lambdawolflabs/FWA-2022-Compass-ConBadge/hardware/design/sims/FWA_2020-2022_Compass_Charlieplex_LED_Currents.asc

19-337_BLU: LED; 19-337_BLU
19-337_GRN: LED; 19-337_GRN
19-337_RED: LED; 19-337_RED
IN-S63BT5UW: LED; IN-S63BT5UW
R1: res; {res}
R2: res; {res}
R3: res; {res}
R4: res; {res}
R5: res; {res}
R6: res; {res}
R7: res; {res}
R8: res; {res}
R9: res; {res}
R10: res; {res}
Resr1: res; {esr}
Resr2: res; {esr}
Resr3: res; {esr}
Resr4: res; {esr}
Resr5: res; {esr}
S1: sw; ATTINY_HS
S2: sw; ATTINY_LS
S3: sw; ATTINY_HS
S4: sw; ATTINY_LS
S5: sw; ATTINY_HS
S6: sw; ATTINY_LS
S7: sw; ATTINY_HS
S8: sw; ATTINY_LS
S9: sw; ATTINY_HS
S10: sw; ATTINY_LS
S11: sw; ATTINY_HS
S12: sw; ATTINY_LS
S13: sw; ATTINY_HS
S14: sw; ATTINY_LS
S15: sw; ATTINY_HS
S16: sw; ATTINY_LS
S17: sw; ATTINY_HS
S18: sw; ATTINY_LS
S19: sw; ATTINY_HS
S20: sw; ATTINY_LS
V1: voltage; 0
V2: voltage; 3
V3: voltage; 3
VLMTG1400: LED; VLMTG1400
Named nets: 0, VCC, L, R
.model ATTINY_HS SW(Ron=40 Roff=50Meg Vt=1.5)
.model ATTINY_LS SW(Roff=30 Ron=50Meg Vt=1.5)
.op
IN-S63BT5UW
VLMTG1400
19-337_RED
19-337_GRN
19-337_BLU
.model 19-337_RED D(Is=1.6137e-10 N=2.979)
.model 19-337_GRN D(Is=1.292e-6 N=7.532)
.model 19-337_BLU D(Is=2.7904E-5 N=9.056)
.MODEL IN-S63BT5UW D(Is=3.8462e-11 N=4.5828)
.MODEL VLMTG1400 D (Is=1.3882e-6 N=6.469)
.model ATTINY_HS_WC SW(Ron=80 Roff=50Meg Vt=1.5)
.model ATTINY_LS_WC SW(Roff=80 Ron=50Meg Vt=1.5)
.param res=82
.param esr=20
