lambdawolflabs/FWA-2022-Compass-ConBadge/hardware/design/sims/FWA_2020-2022_Compass_INT_MUX_Simulation.asc

B1: bv; V=V(VCC)*0.3
B2: bv; V=V(VCC)*0.7
R1: res; 20Meg
R1Leak: res; 20Meg
R2: res; 20Meg
R2Leak: res; 20Meg
R3: res; 1n
R3Leak: res; 20Meg
R4Leak: res; 20Meg
R5Leak: res; 20Meg
R6Leak: res; 20Meg
R13: res; {mc(27k,0.01)}
R14: res; {mc(4.7k,0.012)}
R15: res; {mc(7.5k,0.012)}
S1: sw; LS
S2: sw; LS
S4: sw; LS
V1: voltage; PULSE(3 0 0.5 1n 1n 1 2 2)
V2: voltage; PULSE(3 0 1 1n 1n 1 2 2)
V3: voltage; 3
V4: voltage; PULSE(3 0 0.25 1n 1n 0.5 1.5 4)
Named nets: 0, MAG_INT, NFC_INT, VCC, INT_MUX, ATTINY_VIL, ATTINY_VIH, MAG_DRDY, MAGINT_LOGIC, NFCINT_LOGIC, MAGDRDY_LOGIC
ST25DV04K-IER6S3 GPO Pin
LIS3MDLTR INT Pin (Is indeed an open-drain)
.MODEL LS SW(Roff={ROD} Ron=1G Vt=1.5)
ATTINY414 PA3 Pin
.tran 0 4 0 0.25
.step param run 1 1000 1
https://community.st.com/s/question/0D53W000000A79DSAS/lis3mdltr-data-ready-drdy-on-int-pin
LS is based upon the ST25DV's worst case GPO VOL characteristics
Note: All leakage resistors are based upon the I/O leakage characteriestics of each device.
.step param ROD list 50 200 400
