lambdawolflabs/FWA-2022-Compass-ConBadge/hardware/design/sims/FWA_2020-2022_Compass_Multivibrator_Sim.asc

B1_CR2032: voltage; 3; Rser=20
C1: cap; 10µ
C2: cap; 10µ
C3: cap; 120µ
D1: diode; VLMTG1400
D2: diode; VLMTG1400
D4: diode; VLMTG1400
Q1: npn; 2N2222
Q2: npn; 2N2222
Q3: npn; 2N2222
R1: res; 82
R2: res; 100k
R3: res; 100k
R4: res; 100k
R5: res; 100k
R6: res; 82
R7: res; 100k
R8: res; 82
R9: res; 10Meg
R10: res; 10Meg
Rmeas: res; 1n
Named nets: 0, VBAT, D1_CATHODE, D4_CATHODE, Q1_Collector, Q2_Collector, Q1_B, Q2_B
.tran 0 30 0 0.1
.step param PD list 71.5k 650k 10Meg
.MODEL VLMTG1400 D (Is=1.3882e-6 N=6.469)
